nreinoso23/dibs/docs/images/cad-renders/Inner_Device_Front.PNG

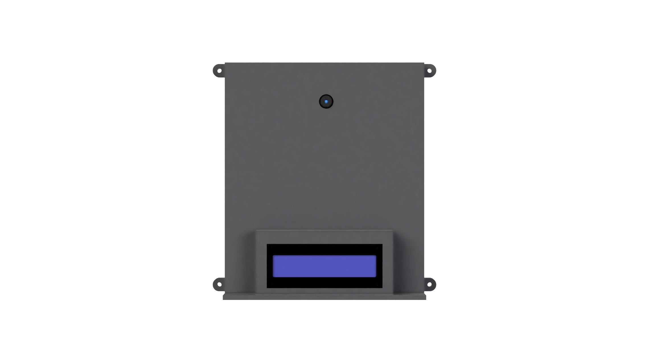
docs/images/cad-renders/Inner_Device_Front.PNG
