nreinoso23/dibs/docs/images/cad-renders/Outer_Device_Front.PNG

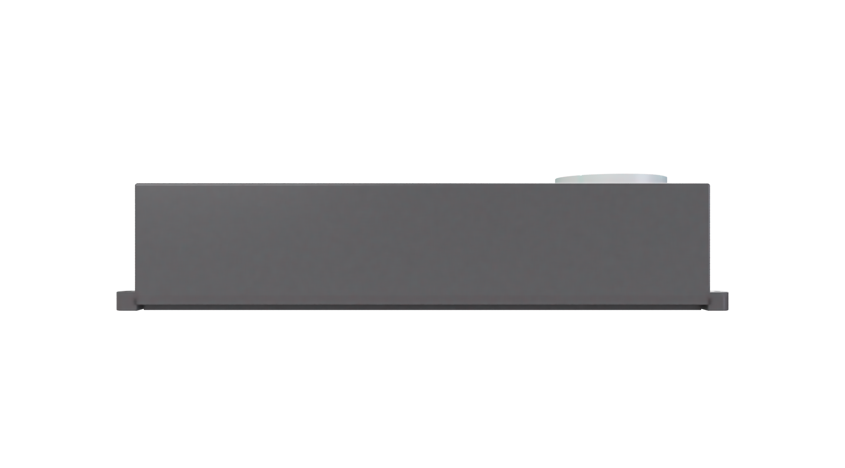
docs/images/cad-renders/Outer_Device_Front.PNG
