nreinoso23/dibs/docs/images/circuit-diagrams/Outer_Circuit_Final.png

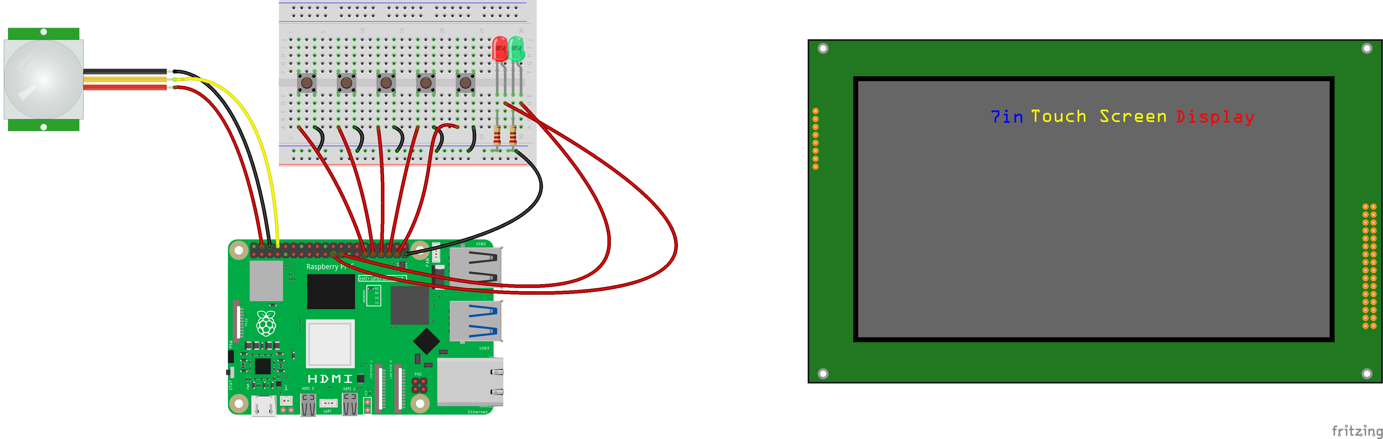
docs/images/circuit-diagrams/Outer_Circuit_Final.png
