nreinoso23/dibs/docs/images/hardware/Outer_Device_Right.JPG

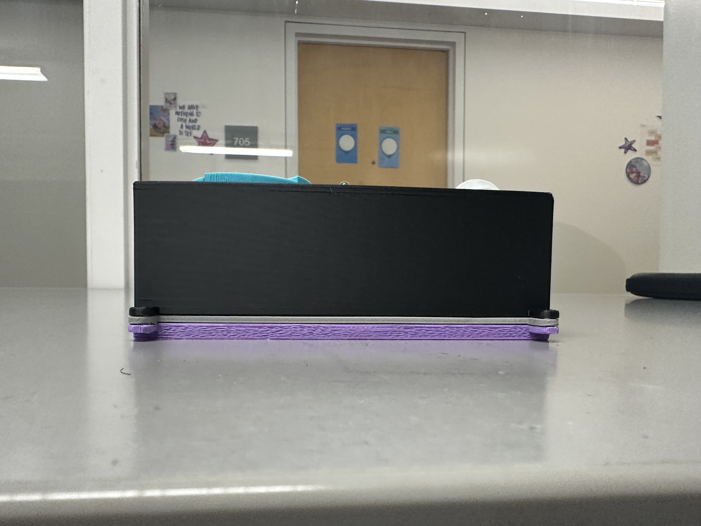
docs/images/hardware/Outer_Device_Right.JPG
