nreinoso23/dibs/docs/screenshot.png

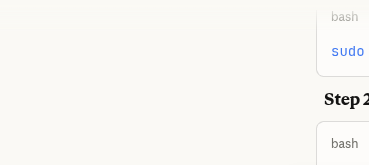
docs/screenshot.png
