nreinoso23/dibs/docs/screenshot_20251123_234622.png

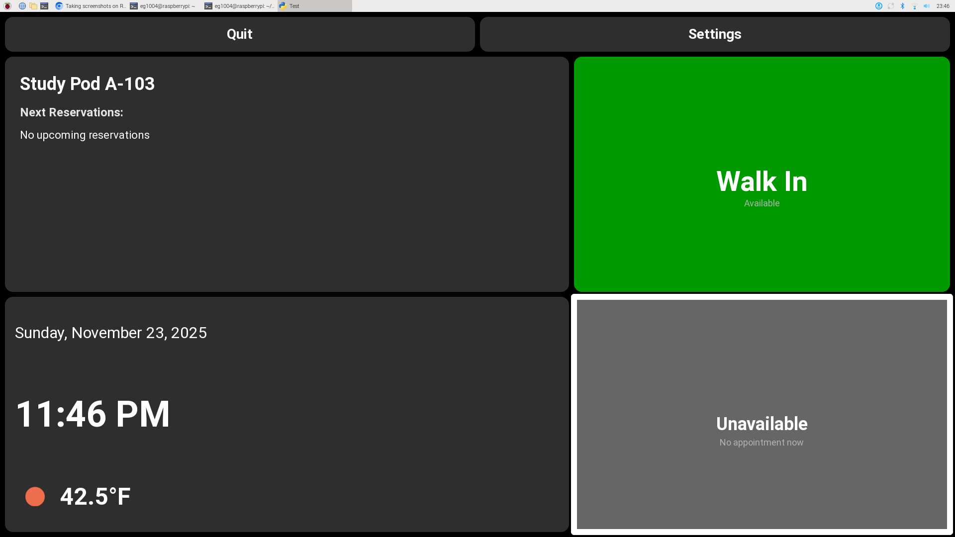
docs/screenshot_20251123_234622.png
