nreinoso23/dibs/docs/screenshot_20251123_234817.png

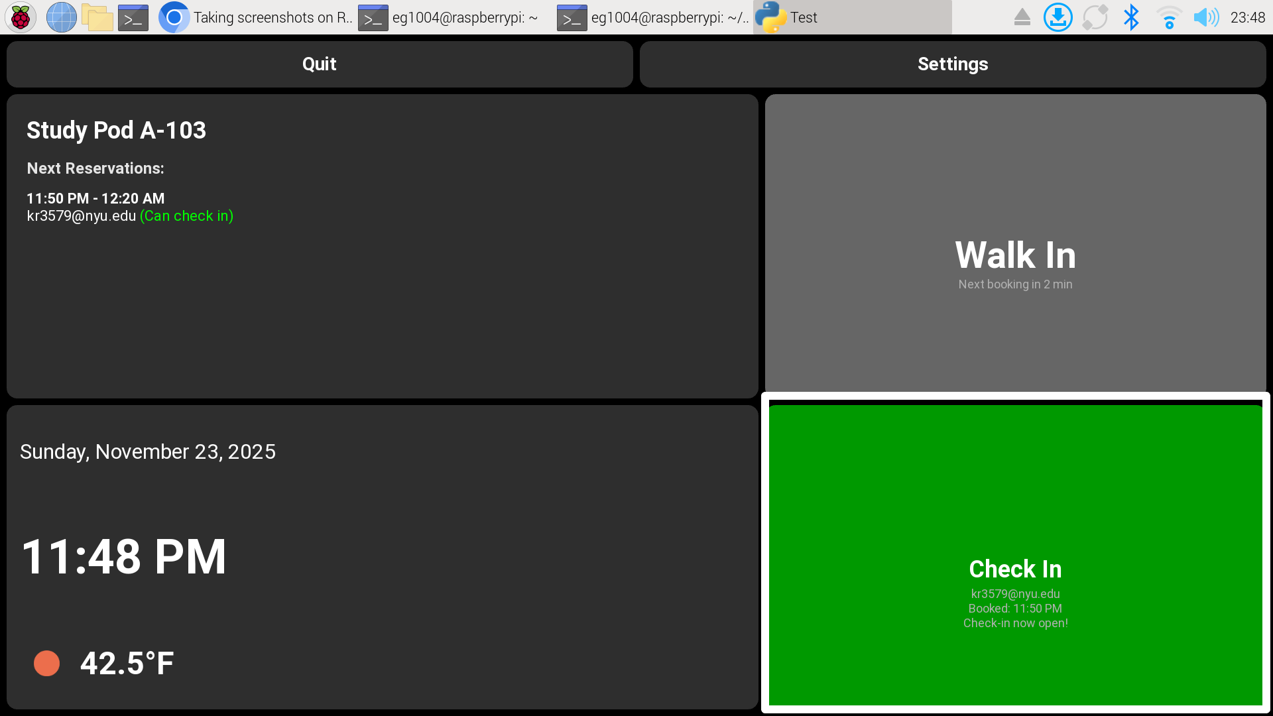
docs/screenshot_20251123_234817.png
